Solaire-42/kers/Software/Figl/STEVAL_SPIN3201_vorne/Src/mc_tasks.c

/**
  ******************************************************************************
  * @file    mc_tasks.c
  * @author  Motor Control SDK Team, ST Microelectronics
  * @brief   This file implements tasks definition
  *
  ******************************************************************************
  * @attention
  *
  * <h2><center>&copy; Copyright (c) 2024 STMicroelectronics.
  * All rights reserved.</center></h2>
  *
  * This software component is licensed by ST under Ultimate Liberty license
  * SLA0044, the "License"; You may not use this file except in compliance with
  * the License. You may obtain a copy of the License at:
  *                             www.st.com/SLA0044
  *
  ******************************************************************************
  */

/* Includes ------------------------------------------------------------------*/
//cstat -MISRAC2012-Rule-21.1
#include "main.h"
//cstat +MISRAC2012-Rule-21.1
#include "mc_type.h"
#include "mc_math.h"
#include "motorcontrol.h"
#include "regular_conversion_manager.h"
#include "mc_interface.h"
#include "digital_output.h"
#include "pwm_common.h"
#include "mc_tasks.h"
#include "parameters_conversion.h"
#include "mcp_config.h"
#include "mc_app_hooks.h"

/* USER CODE BEGIN Private define */
/* Un-Comment this macro define in order to activate the smooth
   braking action on over voltage */
/* #define  MC.SMOOTH_BRAKING_ACTION_ON_OVERVOLTAGE */

/* USER CODE END Private define */

#define VBUS_TEMP_ERR_MASK ~(0 | 0 | MC_OVER_TEMP)

static uint16_t hMFTaskCounterM1 = 0; //cstat !MISRAC2012-Rule-8.9_a
static volatile uint16_t hBootCapDelayCounterM1 = ((uint16_t)0);
static volatile uint16_t hStopPermanencyCounterM1 = ((uint16_t)0);
static volatile uint8_t bMCBootCompleted = ((uint8_t)0);

#define M2_CHARGE_BOOT_CAP_TICKS         (((uint16_t)SYS_TICK_FREQUENCY * (uint16_t)10) / 1000U)
#define M2_CHARGE_BOOT_CAP_DUTY_CYCLES ((uint32_t)0\
                                      * ((uint32_t)PWM_PERIOD_CYCLES2 / 2U))

void TSK_MediumFrequencyTaskM1(void);
void TSK_MF_StopProcessing(uint8_t motor);
MCI_Handle_t *GetMCI(uint8_t bMotor);
void TSK_SetChargeBootCapDelayM1(uint16_t hTickCount);
bool TSK_ChargeBootCapDelayHasElapsedM1(void);
void TSK_SetStopPermanencyTimeM1(uint16_t hTickCount);
bool TSK_StopPermanencyTimeHasElapsedM1(void);
void TSK_SafetyTask_PWMOFF(uint8_t motor);

/**
  * @brief  It initializes the whole MC core according to user defined
  *         parameters.
  * @param  pMCIList pointer to the vector of MCInterface objects that will be
  *         created and initialized. The vector must have length equal to the
  *         number of motor drives.
  */
__weak void MCboot( MCI_Handle_t* pMCIList[NBR_OF_MOTORS] )
{
  if (MC_NULL == pMCIList)
  {
    /* Nothing to do */
  }
  else
  {

    bMCBootCompleted = (uint8_t )0;

    /*************************************************/
    /*    FOC initialization         */
    /*************************************************/
    pMCIList[M1] = &Mci[M1];
    FOC_Init();

    ASPEP_start(&aspepOverUartA);
    /******************************************************/
    /*   PID component initialization: speed regulation   */
    /******************************************************/
    PID_HandleInit(&PIDSpeedHandle_M1);

    /****************************************************/
    /*   Virtual speed sensor component initialization  */
    /****************************************************/
    VSS_Init(&VirtualSpeedSensorM1);

    /********************************************************/
    /*   Bus voltage sensor component initialization        */
    /********************************************************/
    (void)RCM_RegisterRegConv(&VbusRegConv_M1);
    RVBS_Init(&BusVoltageSensor_M1);

    /*******************************************************/
    /*   Temperature measurement component initialization  */
    /*******************************************************/
    NTC_Init(&TempSensor_M1);

    /* Applicative hook in MCBoot() */
    MC_APP_BootHook();

    bMCBootCompleted = 1U;
  }
}

/**
 * @brief Runs all the Tasks of the Motor Control cockpit
 *
 * This function is to be called periodically at least at the Medium Frequency task
 * rate (It is typically called on the Systick interrupt). Exact invokation rate is
 * the Speed regulator execution rate set in the Motor Contorl Workbench.
 *
 * The following tasks are executed in this order:
 *
 * - Medium Frequency Tasks of each motors.
 * - Safety Task.
 * - Power Factor Correction Task (if enabled).
 * - User Interface task.
 */
__weak void MC_RunMotorControlTasks(void)
{
  if (0U == bMCBootCompleted)
  {
    /* Nothing to do */
  }
  else
  {
    /* ** Medium Frequency Tasks ** */
    if(hMFTaskCounterM1 > 0u)
    {
      hMFTaskCounterM1--;
    }
    else
    {
      TSK_MediumFrequencyTaskM1();

      /* Applicative hook at end of Medium Frequency for Motor 1 */
      MC_APP_PostMediumFrequencyHook_M1();

      MCP_Over_UartA.rxBuffer = MCP_Over_UartA.pTransportLayer->fRXPacketProcess(MCP_Over_UartA.pTransportLayer,
                                                                                &MCP_Over_UartA.rxLength);
      if ( 0U == MCP_Over_UartA.rxBuffer)
      {
        /* Nothing to do */
      }
      else
      {
        /* Synchronous answer */
        if (0U == MCP_Over_UartA.pTransportLayer->fGetBuffer(MCP_Over_UartA.pTransportLayer,
                                                     (void **) &MCP_Over_UartA.txBuffer, //cstat !MISRAC2012-Rule-11.3
                                                     MCTL_SYNC))
        {
          /* No buffer available to build the answer ... should not occur */
        }
        else
        {
          MCP_ReceivedPacket(&MCP_Over_UartA);
          MCP_Over_UartA.pTransportLayer->fSendPacket(MCP_Over_UartA.pTransportLayer, MCP_Over_UartA.txBuffer,
                                                      MCP_Over_UartA.txLength, MCTL_SYNC);
          /* No buffer available to build the answer ... should not occur */
        }
      }

      hMFTaskCounterM1 = (uint16_t)MF_TASK_OCCURENCE_TICKS;
    }
    if(hBootCapDelayCounterM1 > 0U)
    {
      hBootCapDelayCounterM1--;
    }
    else
    {
      /* Nothing to do */
    }
    if(hStopPermanencyCounterM1 > 0U)
    {
      hStopPermanencyCounterM1--;
    }
    else
    {
      /* Nothing to do */
    }

    /* Safety task is run after Medium Frequency task so that
     * it can overcome actions they initiated if needed */
    TSK_SafetyTask();

  }
}

/**
  * @brief  It set a counter intended to be used for counting the delay required
  *         for drivers boot capacitors charging of motor 1.
  * @param  hTickCount number of ticks to be counted.
  * @retval void
  */
__weak void TSK_SetChargeBootCapDelayM1(uint16_t hTickCount)
{
   hBootCapDelayCounterM1 = hTickCount;
}

/**
  * @brief  Use this function to know whether the time required to charge boot
  *         capacitors of motor 1 has elapsed.
  * @param  none
  * @retval bool true if time has elapsed, false otherwise.
  */
__weak bool TSK_ChargeBootCapDelayHasElapsedM1(void)
{
  bool retVal = false;
  if (((uint16_t)0) == hBootCapDelayCounterM1)
  {
    retVal = true;
  }
  return (retVal);
}

/**
  * @brief  It set a counter intended to be used for counting the permanency
  *         time in STOP state of motor 1.
  * @param  hTickCount number of ticks to be counted.
  * @retval void
  */
__weak void TSK_SetStopPermanencyTimeM1(uint16_t hTickCount)
{
  hStopPermanencyCounterM1 = hTickCount;
}

/**
  * @brief  Use this function to know whether the permanency time in STOP state
  *         of motor 1 has elapsed.
  * @param  none
  * @retval bool true if time is elapsed, false otherwise.
  */
__weak bool TSK_StopPermanencyTimeHasElapsedM1(void)
{
  bool retVal = false;
  if (((uint16_t)0) == hStopPermanencyCounterM1)
  {
    retVal = true;
  }
  return (retVal);
}

#if defined (CCMRAM)
#if defined (__ICCARM__)
#pragma location = ".ccmram"
#elif defined (__CC_ARM) || defined(__GNUC__)
__attribute__((section (".ccmram")))
#endif
#endif

/**
  * @brief  Executes the Motor Control duties that require a high frequency rate and a precise timing.
  *
  *  This is mainly the FOC current control loop. It is executed depending on the state of the Motor Control
  * subsystem (see the state machine(s)).
  *
  * @retval Number of the  motor instance which FOC loop was executed.
  */
__weak uint8_t TSK_HighFrequencyTask(void)
{
  uint8_t bMotorNbr;
  bMotorNbr = 0;

  FOC_HighFrequencyTask(bMotorNbr);

  return (bMotorNbr);

}

/**
  * @brief  Executes safety checks (e.g. bus voltage and temperature) for all drive instances.
  *
  * Faults flags are updated here.
  */
__weak void TSK_SafetyTask(void)
{
  if (1U == bMCBootCompleted)
  {
    TSK_SafetyTask_PWMOFF(M1);
    /* User conversion execution */
    RCM_ExecUserConv();
  }
  else
  {
    /* Nothing to do */
  }
}

/**
  * @brief  Safety task implementation if  MC.M1_ON_OVER_VOLTAGE == TURN_OFF_PWM.
  * @param  bMotor Motor reference number defined
  *         \link Motors_reference_number here \endlink.
  */
__weak void TSK_SafetyTask_PWMOFF(uint8_t bMotor)
{
  uint16_t CodeReturn = MC_NO_ERROR;
  uint8_t lbmotor = M1;
  const uint16_t errMask[NBR_OF_MOTORS] = {VBUS_TEMP_ERR_MASK};
  /* Check for fault if FW protection is activated. It returns MC_OVER_TEMP or MC_NO_ERROR */

/* Due to warning array subscript 1 is above array bounds of PWMC_Handle_t *[1] [-Warray-bounds] */
   CodeReturn |= PWMC_IsFaultOccurred(pwmcHandle[lbmotor]);     /* check for fault. It return MC_OVER_CURR or MC_NO_FAULTS
                                                     (for STM32F30x can return MC_OVER_VOLT in case of HW Overvoltage) */

  if (M1 == bMotor)
  {
    uint16_t rawValueM1 =  RCM_ExecRegularConv(&VbusRegConv_M1);
    CodeReturn |= errMask[bMotor] & RVBS_CalcAvVbus(&BusVoltageSensor_M1, rawValueM1);
  }
  else
  {
    /* Nothing to do */
  }
  MCI_FaultProcessing(&Mci[bMotor], CodeReturn, ~CodeReturn); /* Process faults */

  if (MCI_GetFaultState(&Mci[bMotor]) != (uint32_t)MC_NO_FAULTS)
  {
    PWMC_SwitchOffPWM(pwmcHandle[bMotor]);
    FOC_Clear(bMotor);
  }
  else
  {
    /* No errors */
  }
}

/**
  * @brief  Puts the Motor Control subsystem in in safety conditions on a Hard Fault
  *
  *  This function is to be executed when a general hardware failure has been detected
  * by the microcontroller and is used to put the system in safety condition.
  */
__weak void TSK_HardwareFaultTask(void)
{
   FOC_Clear(M1);
  MCI_FaultProcessing(&Mci[M1], MC_SW_ERROR, 0);

}

__weak void UI_HandleStartStopButton_cb (void)
{
/* USER CODE BEGIN START_STOP_BTN */
  if (IDLE == MC_GetSTMStateMotor1())
  {
    /* Ramp parameters should be tuned for the actual motor */
    (void)MC_StartMotor1();
  }
  else
  {
    (void)MC_StopMotor1();
  }
/* USER CODE END START_STOP_BTN */
}

 /**
  * @brief  Locks GPIO pins used for Motor Control to prevent accidental reconfiguration.
  */
__weak void mc_lock_pins (void)
{
LL_GPIO_LockPin(M1_CURR_AMPL_W_GPIO_Port, M1_CURR_AMPL_W_Pin);
LL_GPIO_LockPin(M1_CURR_AMPL_U_GPIO_Port, M1_CURR_AMPL_U_Pin);
LL_GPIO_LockPin(M1_CURR_AMPL_V_GPIO_Port, M1_CURR_AMPL_V_Pin);
LL_GPIO_LockPin(M1_BUS_VOLTAGE_GPIO_Port, M1_BUS_VOLTAGE_Pin);
LL_GPIO_LockPin(M1_PWM_UH_GPIO_Port, M1_PWM_UH_Pin);
LL_GPIO_LockPin(M1_PWM_VH_GPIO_Port, M1_PWM_VH_Pin);
LL_GPIO_LockPin(M1_OCP_GPIO_Port, M1_OCP_Pin);
LL_GPIO_LockPin(M1_PWM_VL_GPIO_Port, M1_PWM_VL_Pin);
LL_GPIO_LockPin(M1_PWM_WH_GPIO_Port, M1_PWM_WH_Pin);
LL_GPIO_LockPin(M1_PWM_WL_GPIO_Port, M1_PWM_WL_Pin);
LL_GPIO_LockPin(M1_PWM_UL_GPIO_Port, M1_PWM_UL_Pin);
}
/******************* (C) COPYRIGHT 2024 STMicroelectronics *****END OF FILE****/
